tristenpayne2020-web/Grille-talk-keychains/kc/cars/amg_gt63_4door/ref/front.jpg

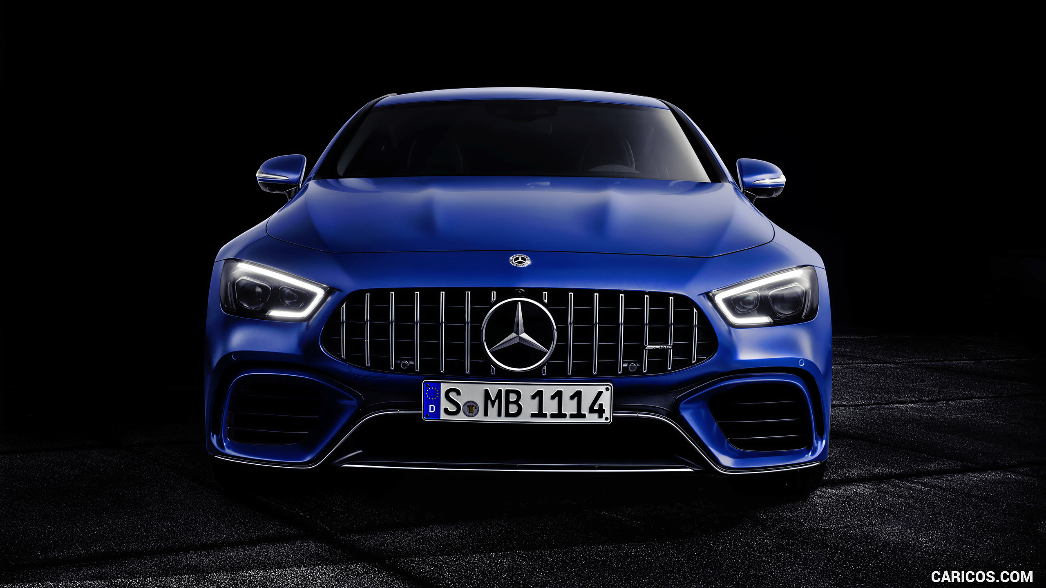
kc/cars/amg_gt63_4door/ref/front.jpg
