tristenpayne2020-web/Grille-talk-keychains/kc/cars/bugatti_chiron/ref/front.jpg

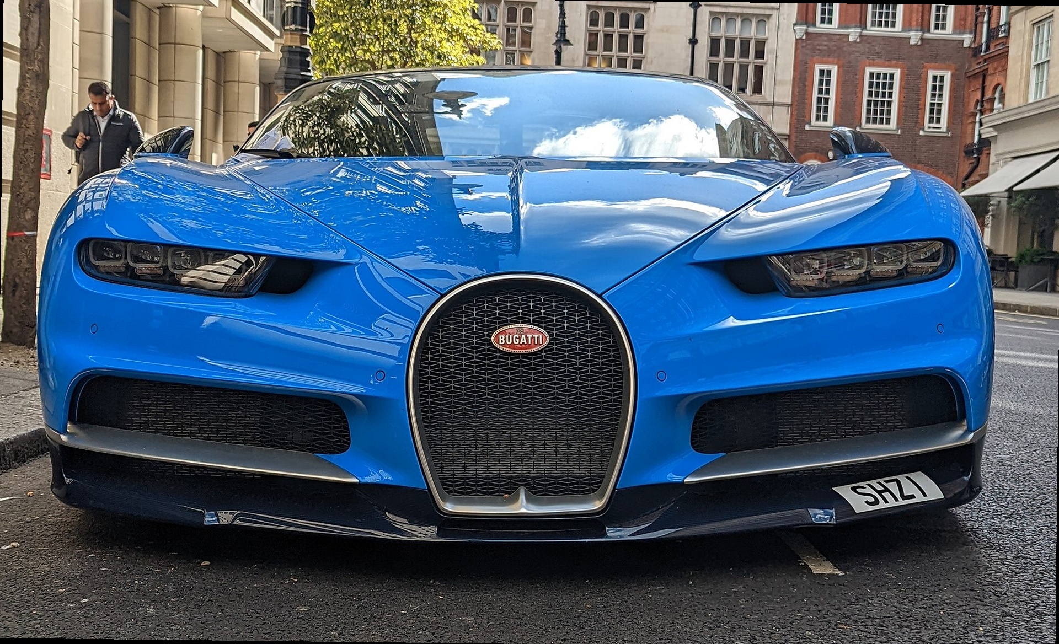
kc/cars/bugatti_chiron/ref/front.jpg
