tristenpayne2020-web/Grille-talk-keychains/kc/cars/c7_z06/ref/cand_blue_show.jpg

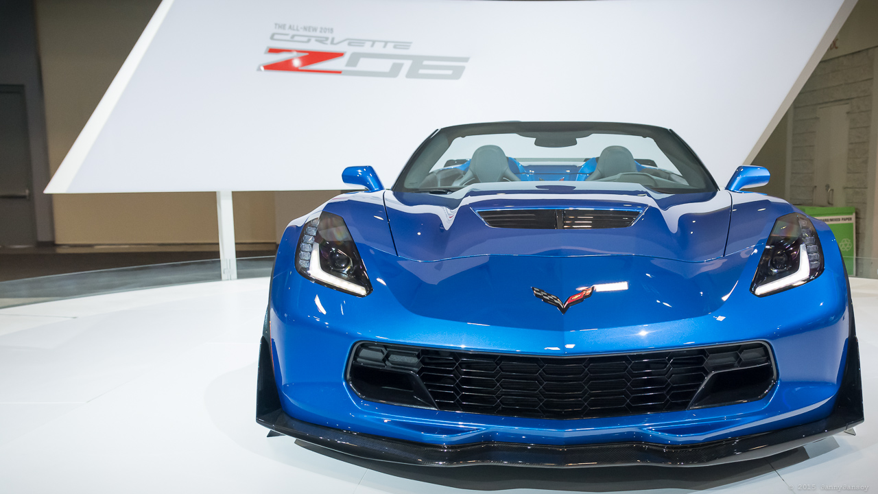
kc/cars/c7_z06/ref/cand_blue_show.jpg
