tristenpayne2020-web/Grille-talk-keychains/kc/cars/c7_z06/ref/front_raw.jpg

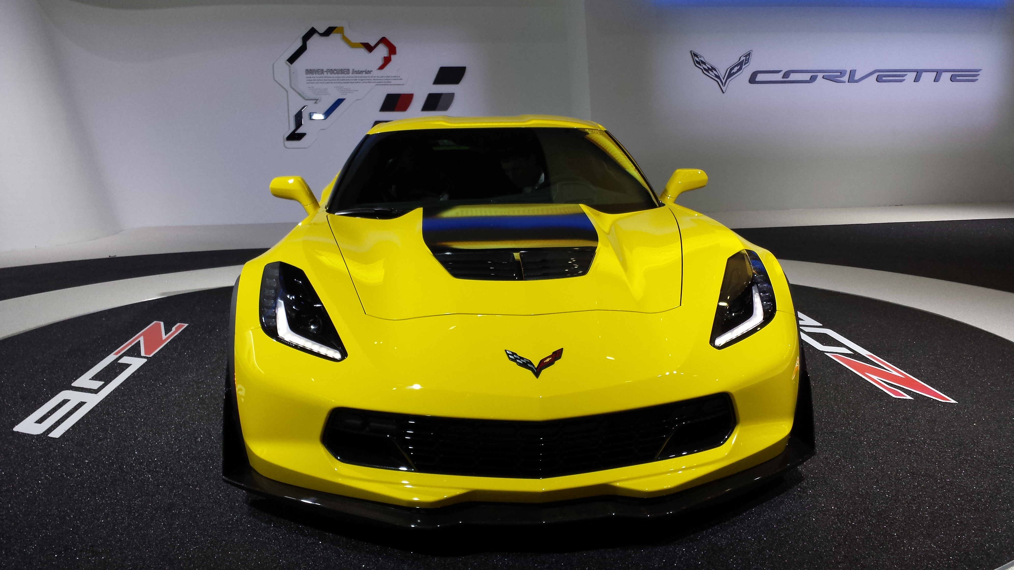
kc/cars/c7_z06/ref/front_raw.jpg
