tristenpayne2020-web/Grille-talk-keychains/kc/cars/c8_corvette/ref/front.jpg

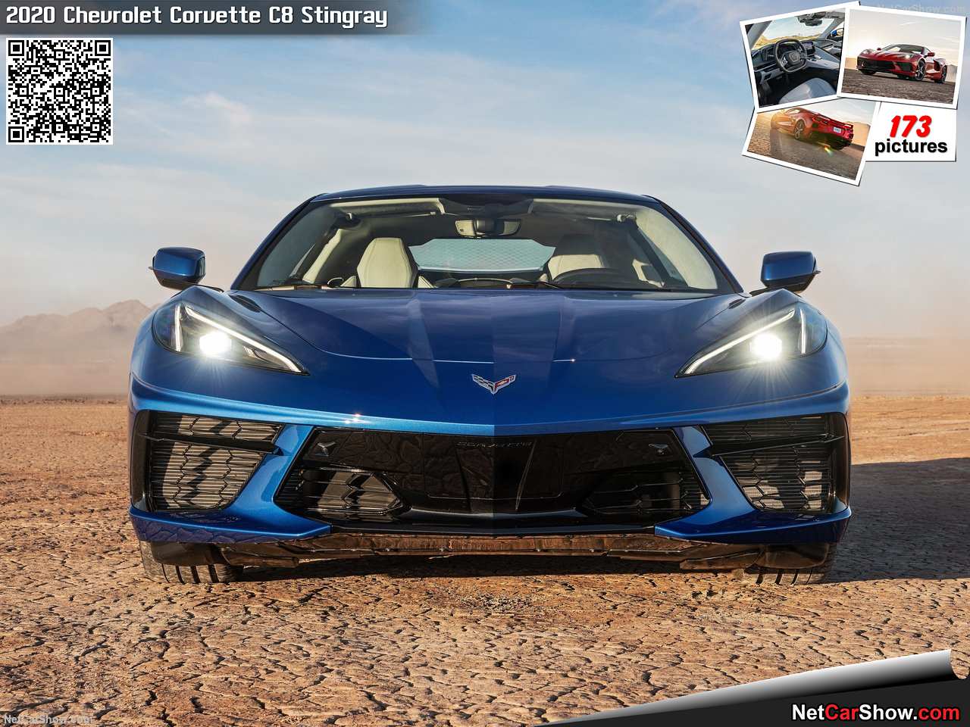
kc/cars/c8_corvette/ref/front.jpg
