tristenpayne2020-web/Grille-talk-keychains/kc/cars/camaro_zl1/ref/front.jpg

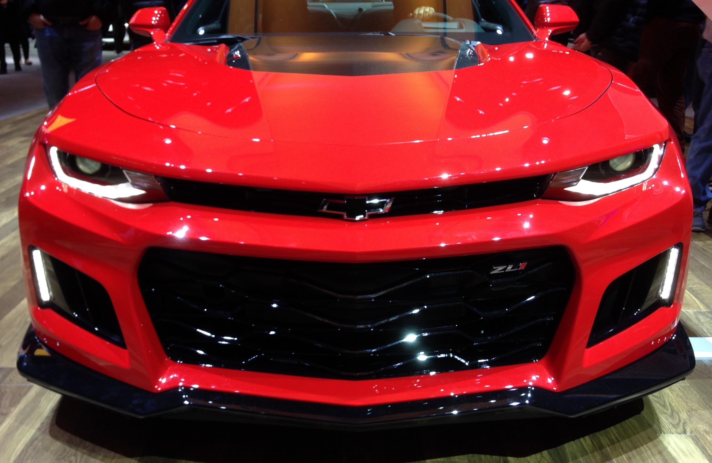
kc/cars/camaro_zl1/ref/front.jpg
