tristenpayne2020-web/Grille-talk-keychains/kc/cars/challenger_hellcat/ref/front.jpg

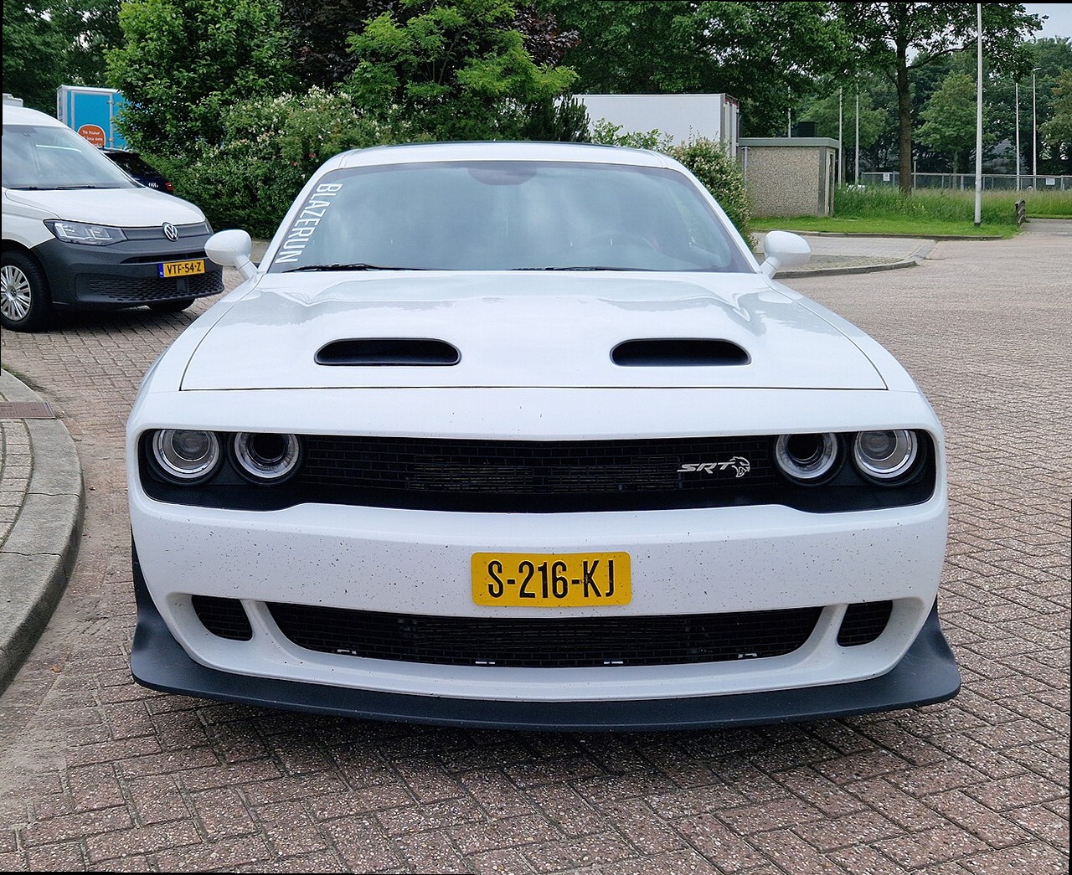
kc/cars/challenger_hellcat/ref/front.jpg
