tristenpayne2020-web/Grille-talk-keychains/kc/cars/charger_srt/ref/front.jpg

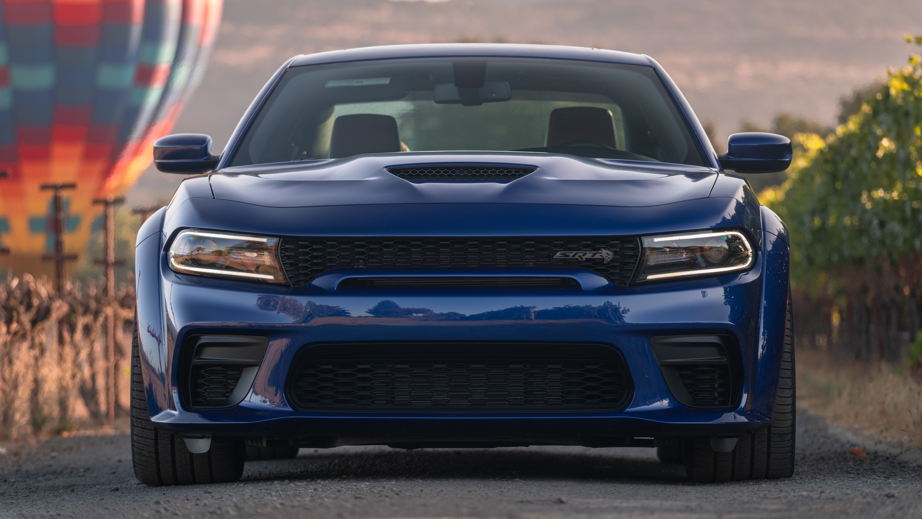
kc/cars/charger_srt/ref/front.jpg
