tristenpayne2020-web/Grille-talk-keychains/kc/cars/civic_11th/ref/front.jpg

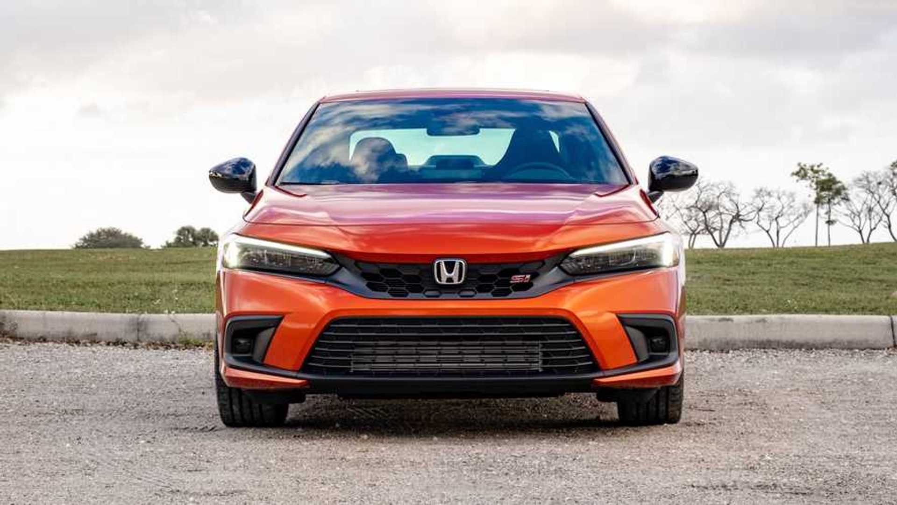
kc/cars/civic_11th/ref/front.jpg
