tristenpayne2020-web/Grille-talk-keychains/kc/cars/ct5v_blackwing/ref/front.jpg

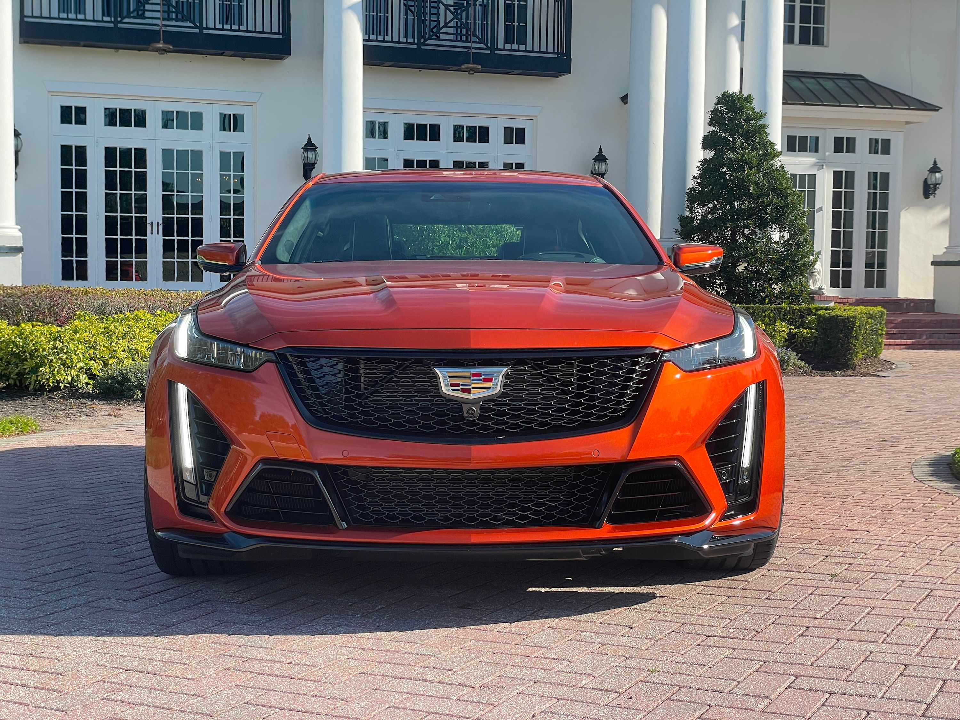
kc/cars/ct5v_blackwing/ref/front.jpg
