tristenpayne2020-web/Grille-talk-keychains/kc/cars/e30_m3/ref/front.jpg

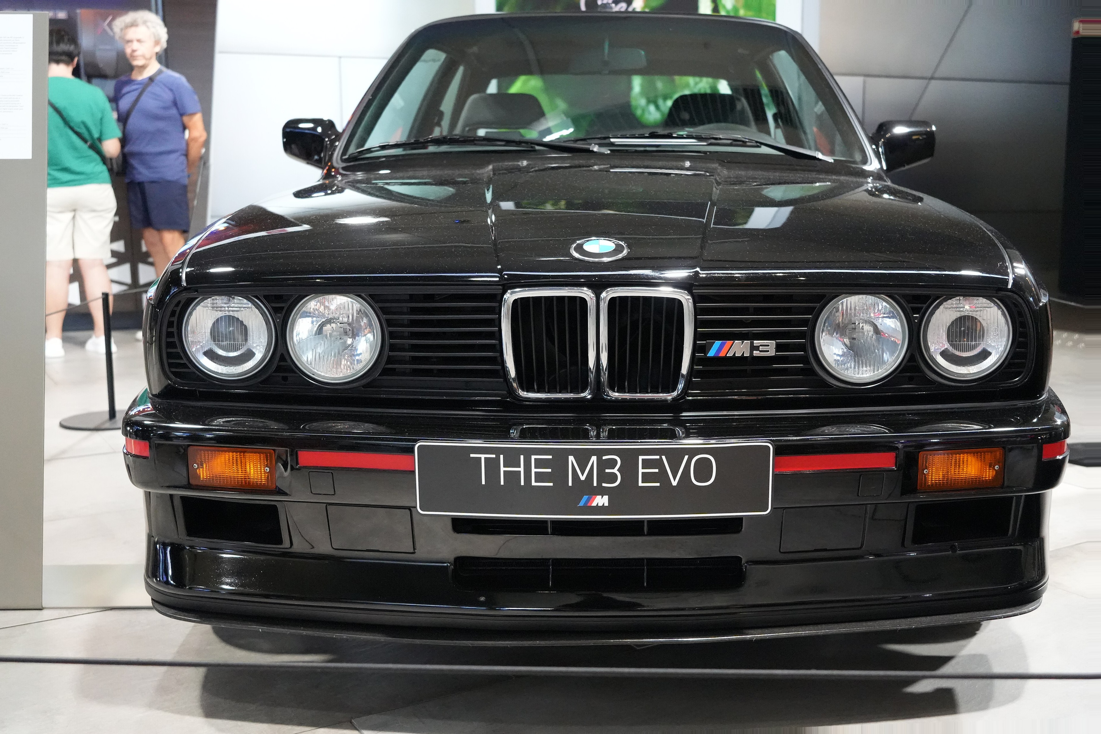
kc/cars/e30_m3/ref/front.jpg
