tristenpayne2020-web/Grille-talk-keychains/kc/cars/f82_m4/ref/front.jpg

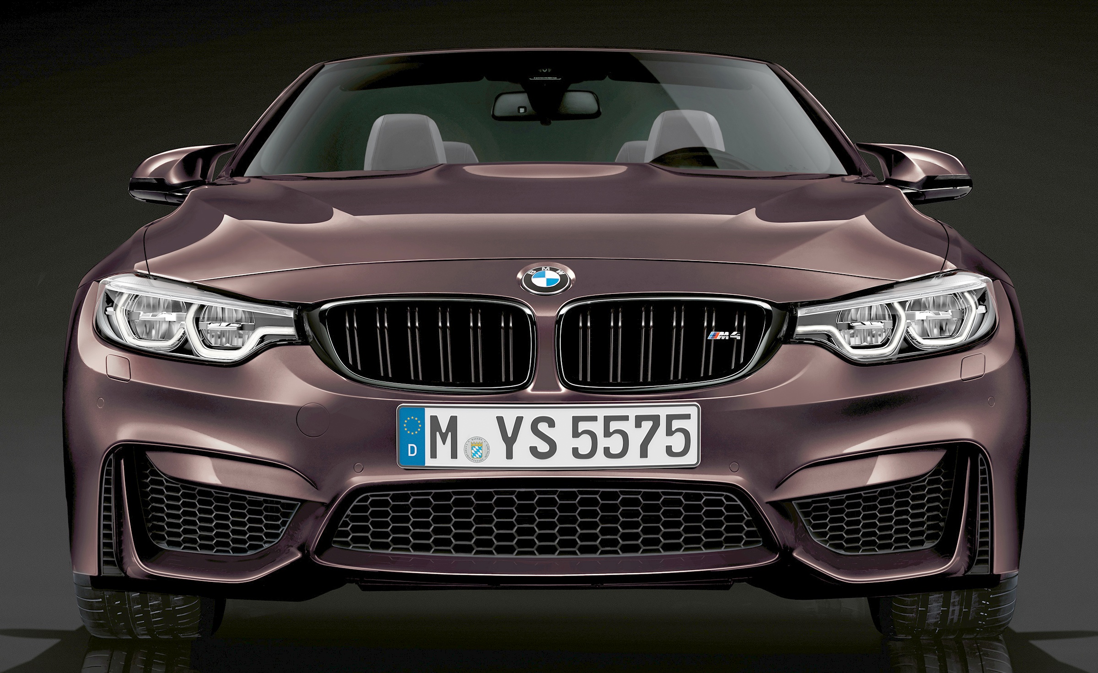
kc/cars/f82_m4/ref/front.jpg
