tristenpayne2020-web/Grille-talk-keychains/kc/cars/f87_m2/ref/front.jpg

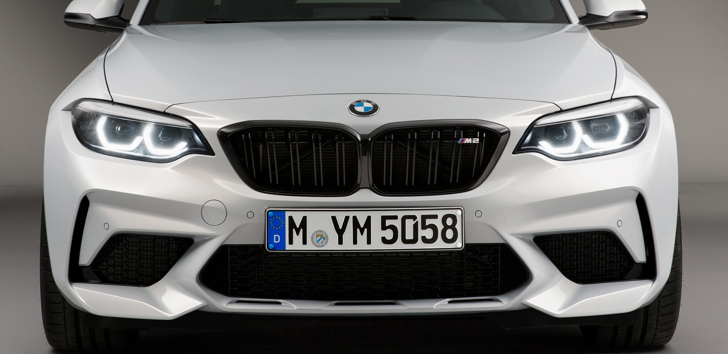
kc/cars/f87_m2/ref/front.jpg
