tristenpayne2020-web/Grille-talk-keychains/kc/cars/f92_m8/ref/front_level.jpg

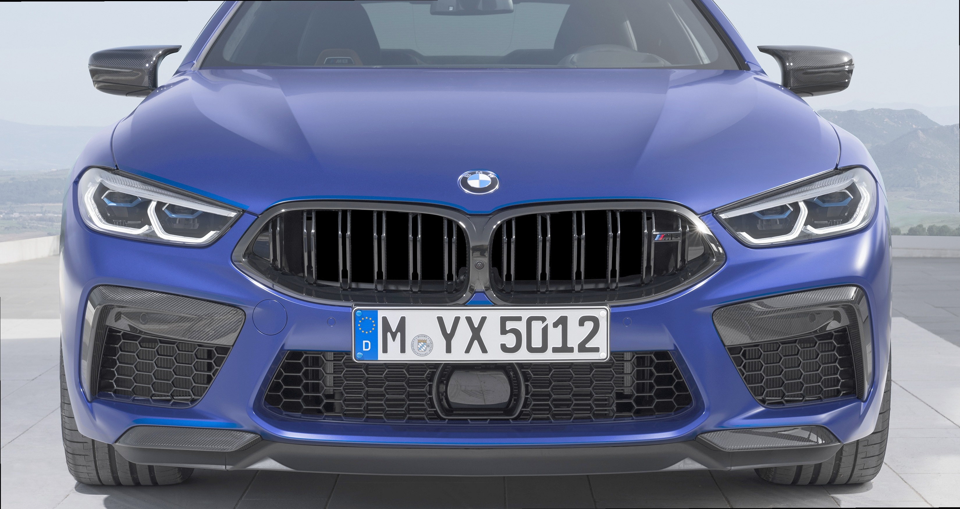
kc/cars/f92_m8/ref/front_level.jpg
