tristenpayne2020-web/Grille-talk-keychains/kc/cars/g20_m340i_lci/ref/front.jpg

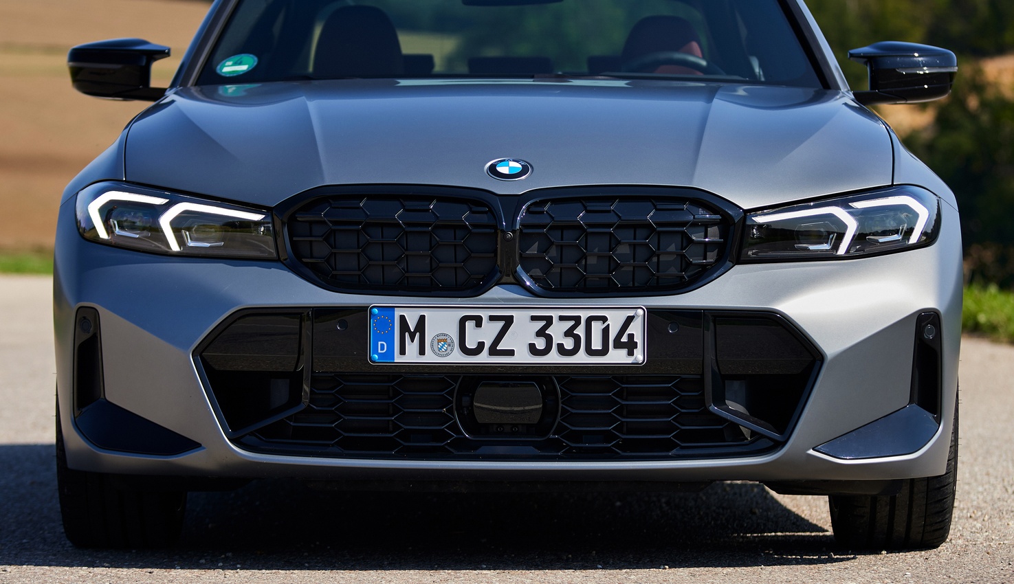
kc/cars/g20_m340i_lci/ref/front.jpg
