tristenpayne2020-web/Grille-talk-keychains/kc/cars/g42_m240i_lci/ref/front.jpg

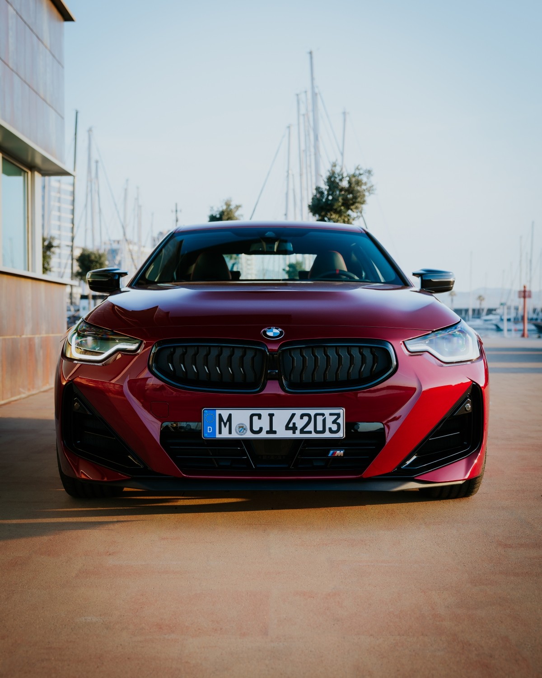
kc/cars/g42_m240i_lci/ref/front.jpg
