tristenpayne2020-web/Grille-talk-keychains/kc/cars/g87_m2/ref/front_warped.png

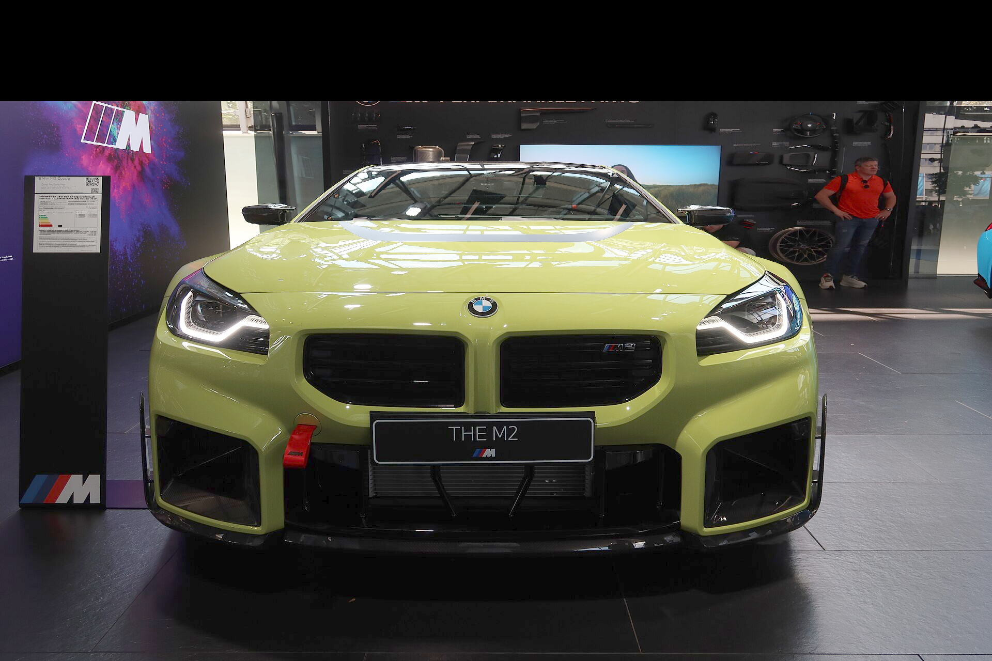
kc/cars/g87_m2/ref/front_warped.png
