tristenpayne2020-web/Grille-talk-keychains/kc/cars/gr86/ref/front.jpg

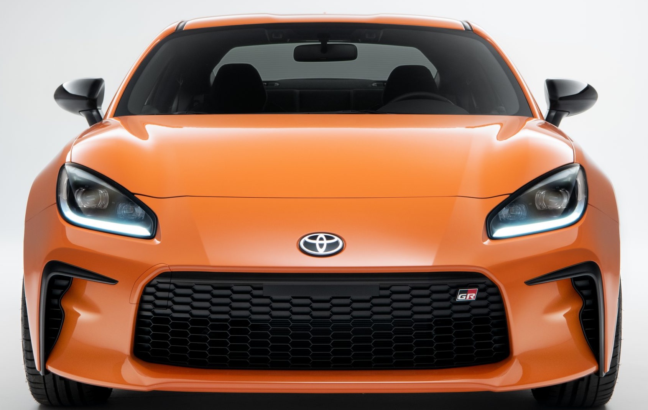
kc/cars/gr86/ref/front.jpg
