tristenpayne2020-web/Grille-talk-keychains/kc/cars/gt3rs_992/ref/front.jpg

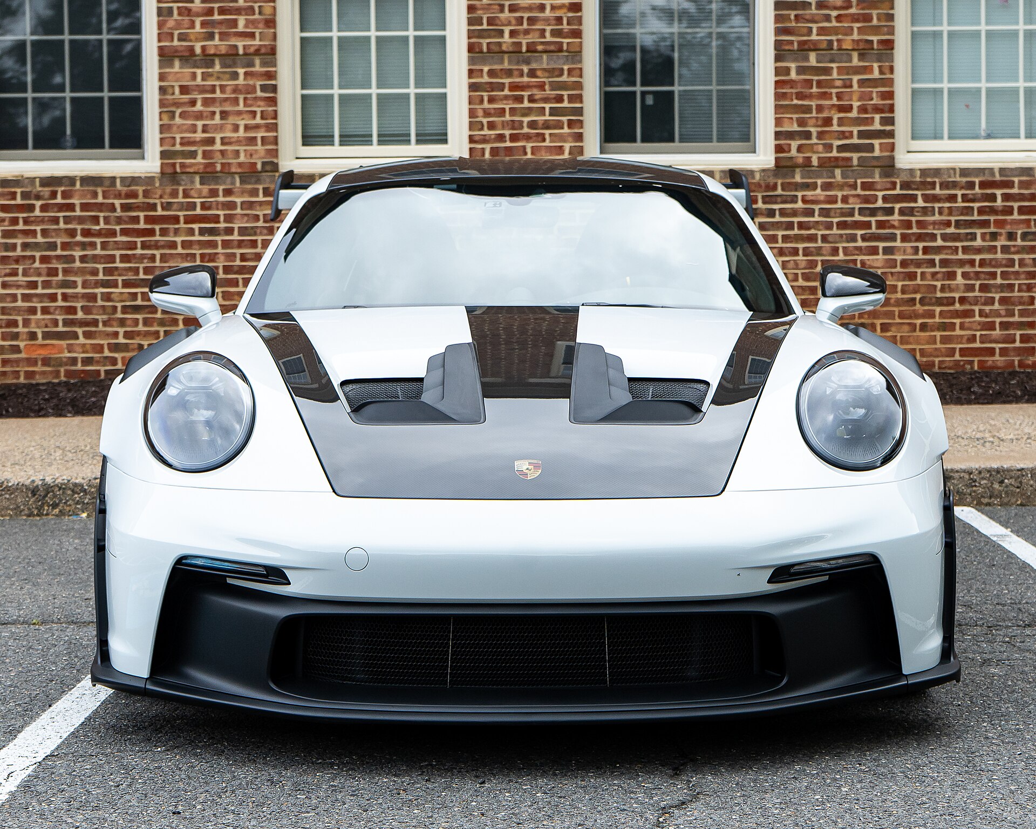
kc/cars/gt3rs_992/ref/front.jpg
