tristenpayne2020-web/Grille-talk-keychains/kc/cars/gt500_mustang/ref/front.jpg

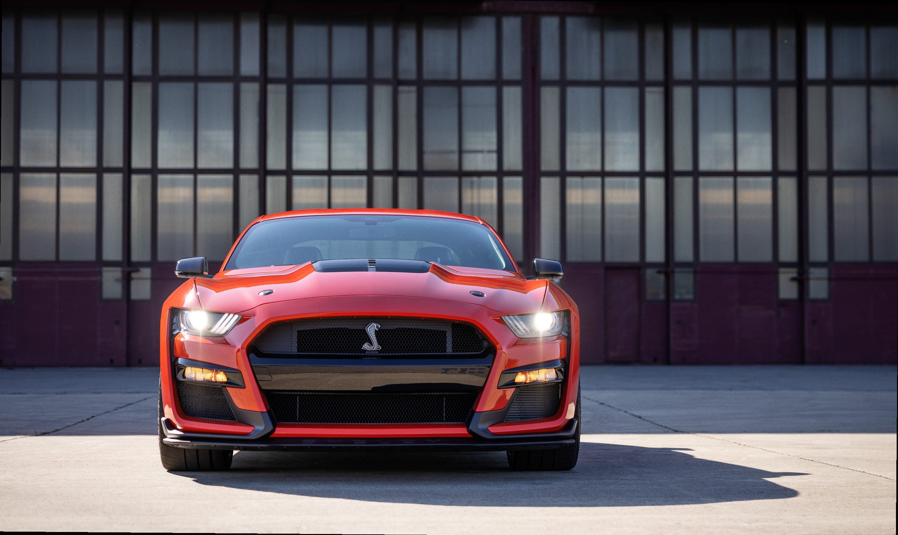
kc/cars/gt500_mustang/ref/front.jpg
