tristenpayne2020-web/Grille-talk-keychains/kc/cars/lambo_urus/ref/front.jpg

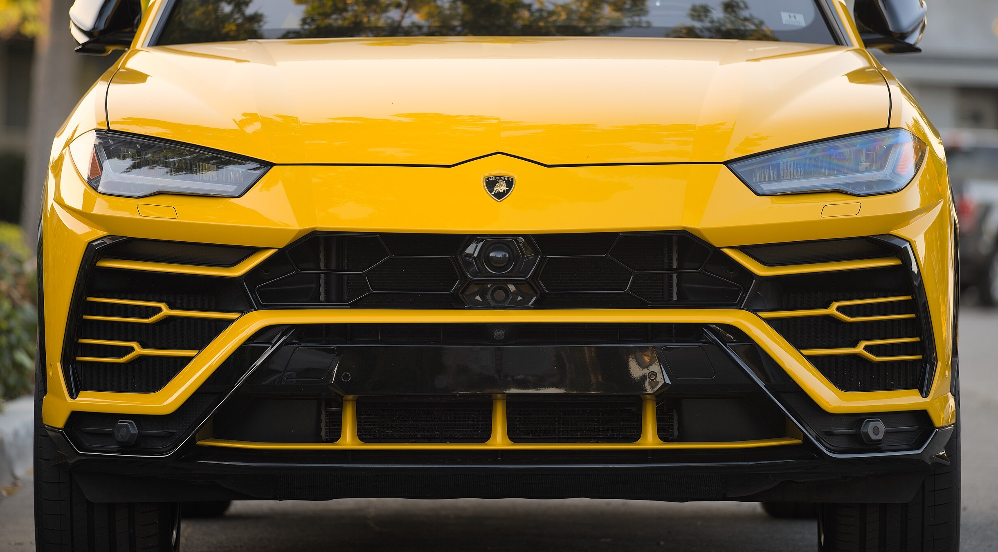
kc/cars/lambo_urus/ref/front.jpg
