tristenpayne2020-web/Grille-talk-keychains/kc/cars/lexus_is350/ref/front.jpg

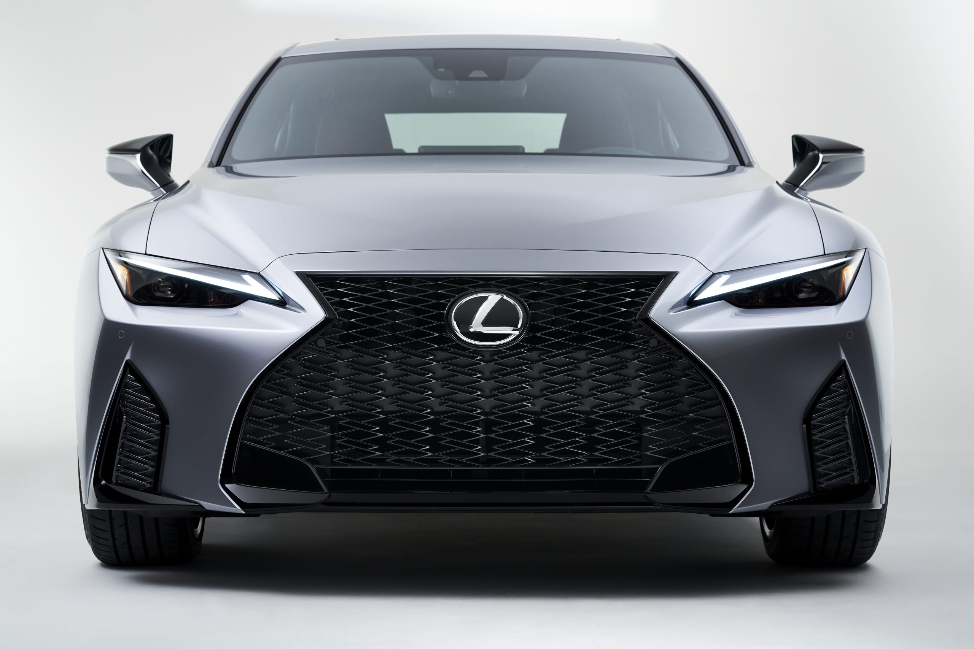
kc/cars/lexus_is350/ref/front.jpg
