tristenpayne2020-web/Grille-talk-keychains/kc/cars/mclaren_720s/ref/front.jpg

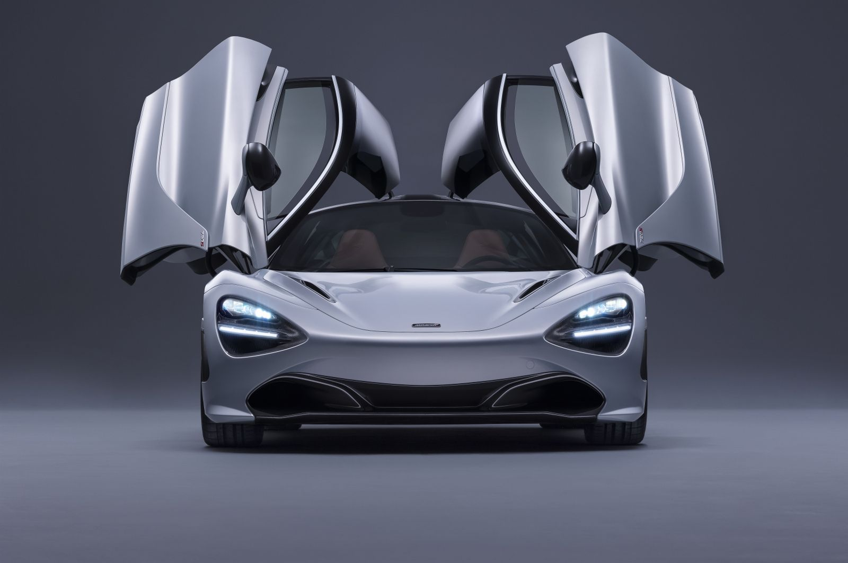
kc/cars/mclaren_720s/ref/front.jpg
