tristenpayne2020-web/Grille-talk-keychains/kc/cars/mk5_supra/ref/front.jpg

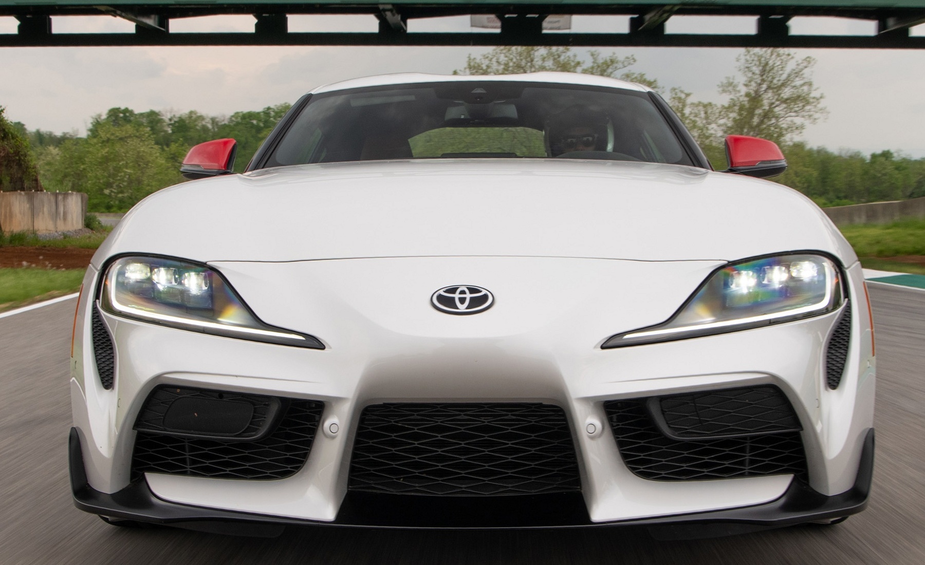
kc/cars/mk5_supra/ref/front.jpg
