tristenpayne2020-web/Grille-talk-keychains/kc/cars/r8_audi/ref/front.jpg

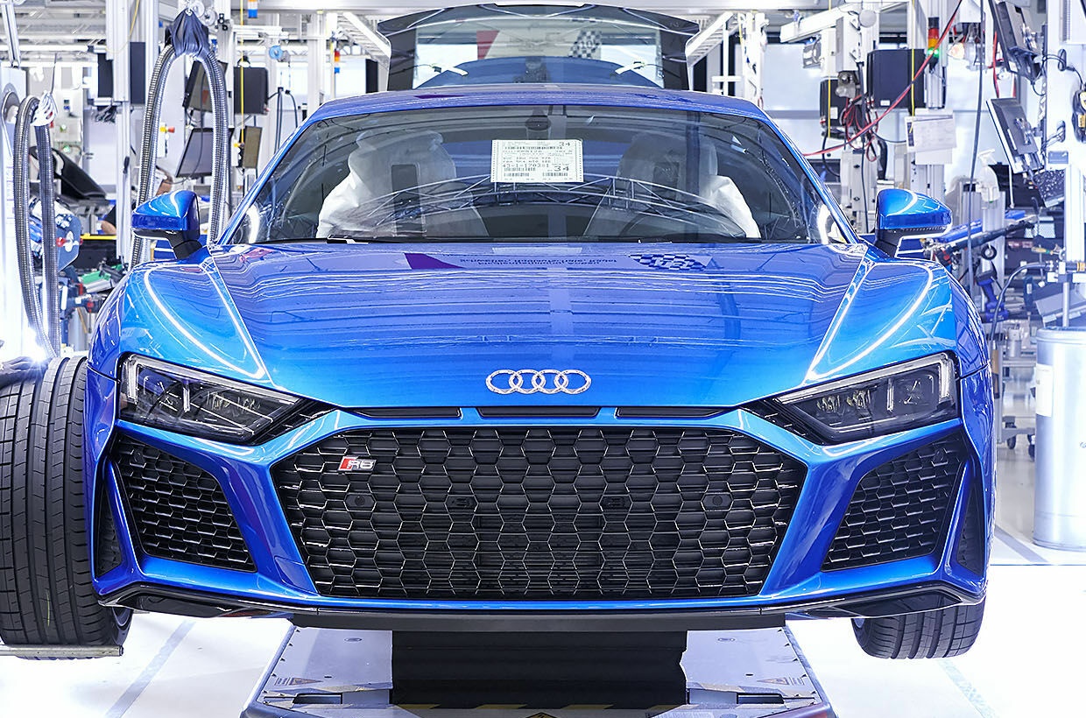
kc/cars/r8_audi/ref/front.jpg
