tristenpayne2020-web/Grille-talk-keychains/kc/cars/r35_gtr/ref/front.jpg

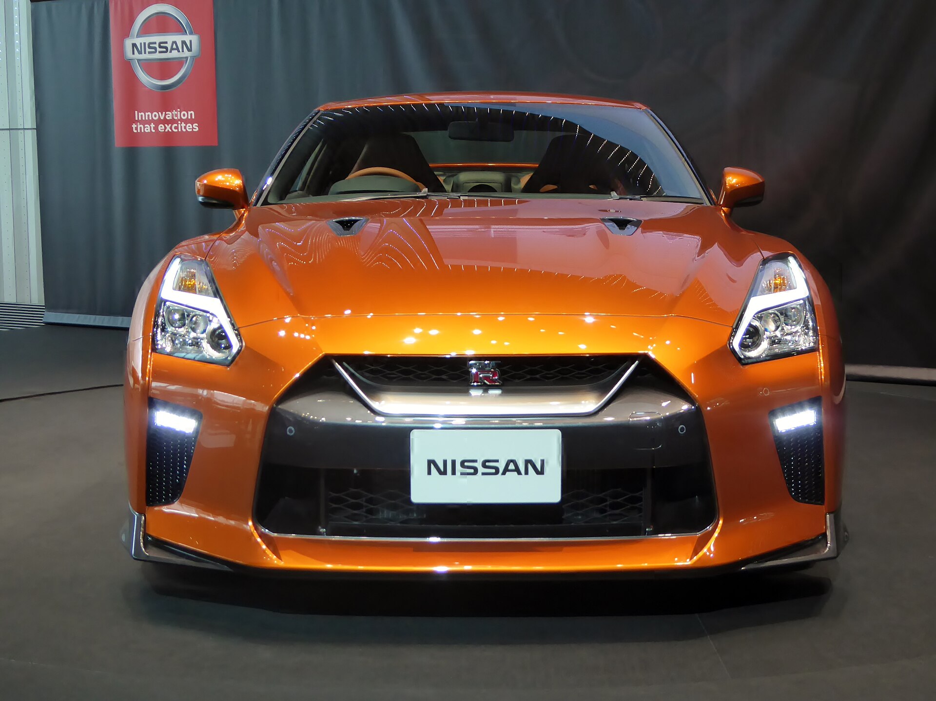
kc/cars/r35_gtr/ref/front.jpg
