tristenpayne2020-web/Grille-talk-keychains/kc/cars/r35_gtr/ref/front_hood085.jpg

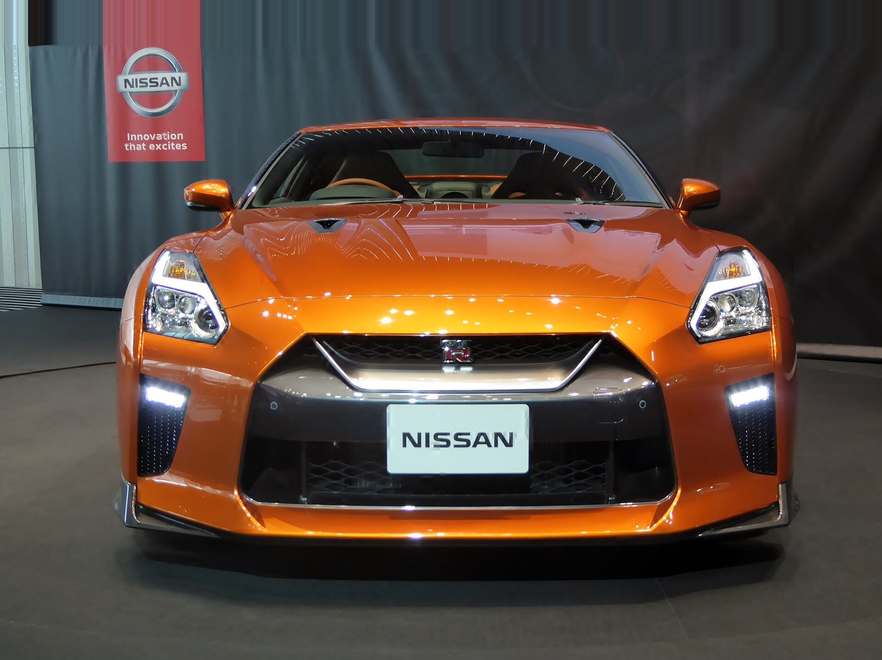
kc/cars/r35_gtr/ref/front_hood085.jpg
