tristenpayne2020-web/Grille-talk-keychains/kc/cars/s650_mustang/ref/front.jpg

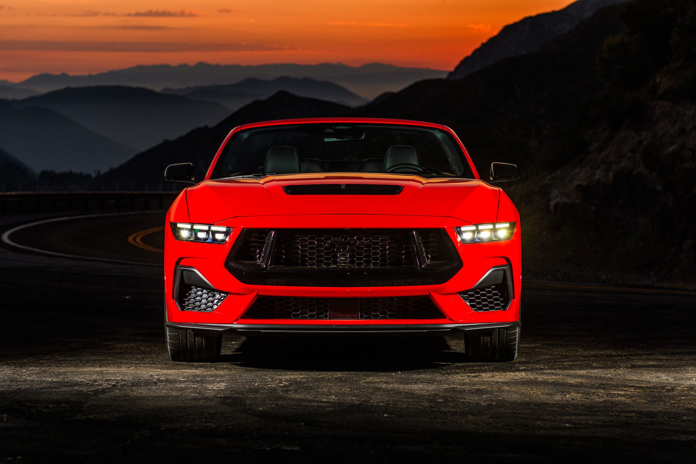
kc/cars/s650_mustang/ref/front.jpg
