tristenpayne2020-web/Grille-talk-keychains/kc/cars/svj_aventador/ref/alt_red_monaco_1146.jpg

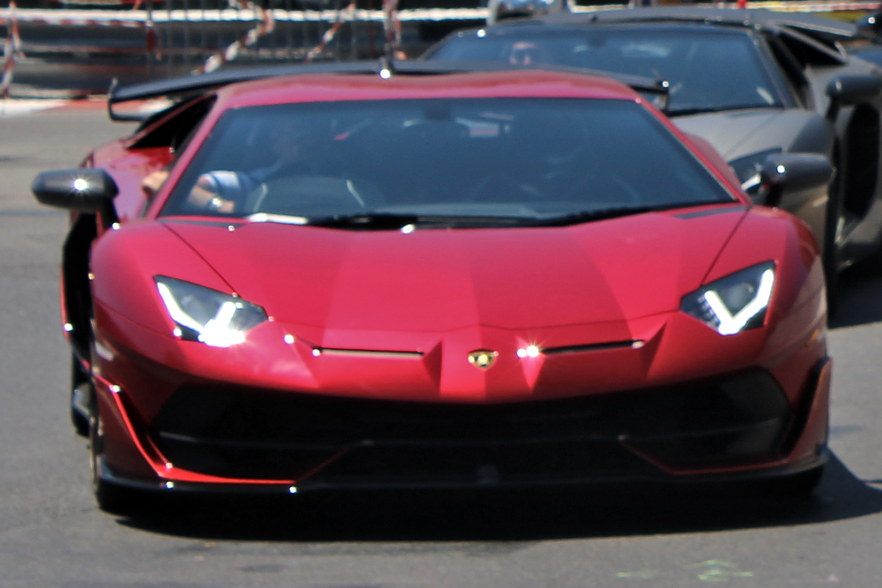
kc/cars/svj_aventador/ref/alt_red_monaco_1146.jpg
