tristenpayne2020-web/Grille-talk-keychains/kc/cars/svj_aventador/ref/front.jpg

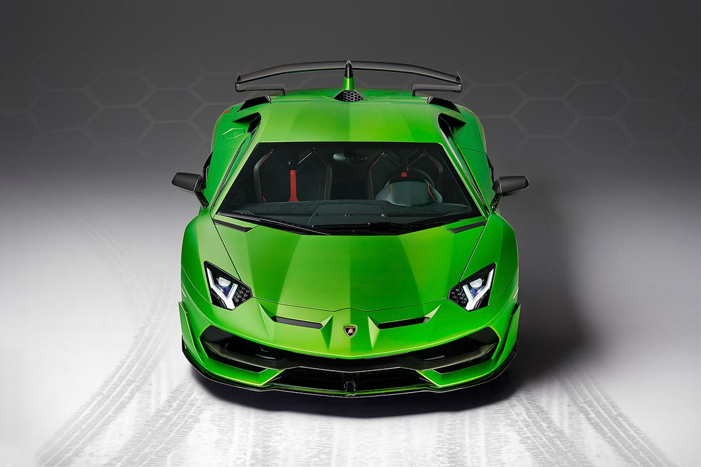
kc/cars/svj_aventador/ref/front.jpg
