tristenpayne2020-web/Grille-talk-keychains/kc/cars/svj_aventador/ref/front_elev.png

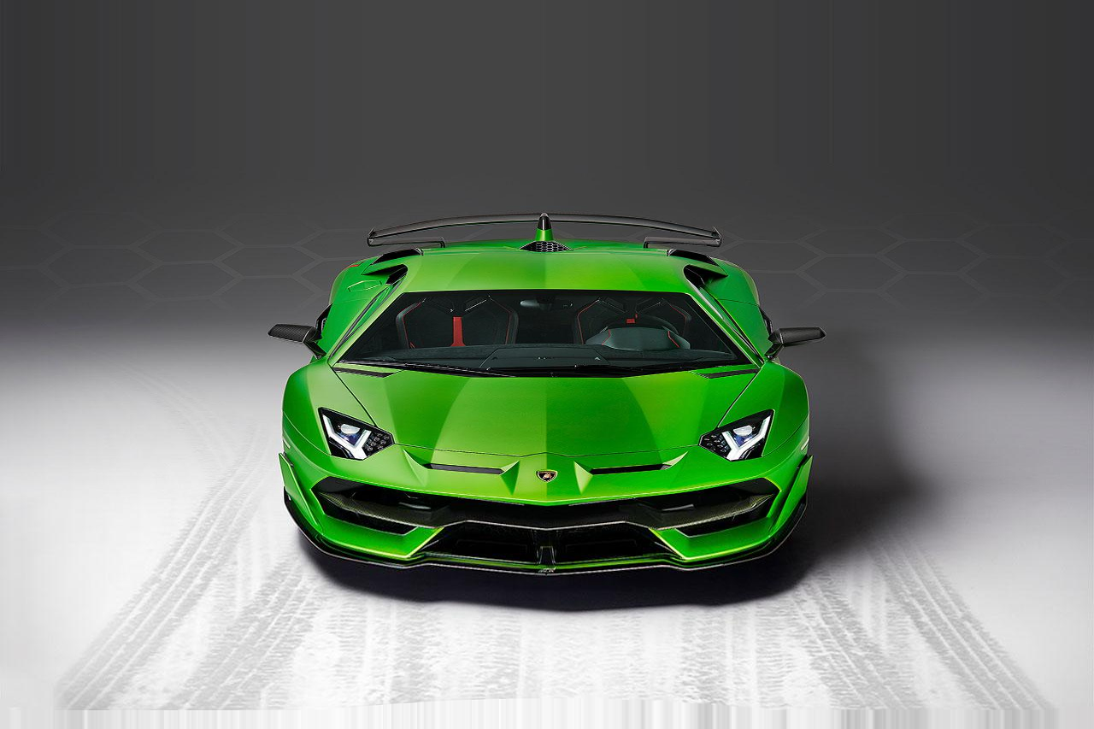
kc/cars/svj_aventador/ref/front_elev.png
