tristenpayne2020-web/Grille-talk-keychains/kc/cars/zonda_cinque/ref/front_press.jpg

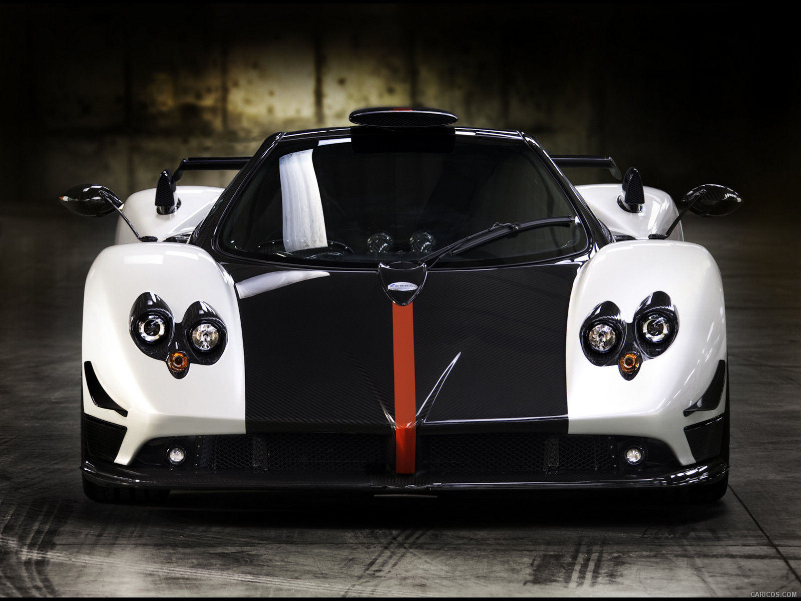
kc/cars/zonda_cinque/ref/front_press.jpg
