tristenpayne2020-web/Grille-talk-keychains/kc/style/g80_face_flat.png

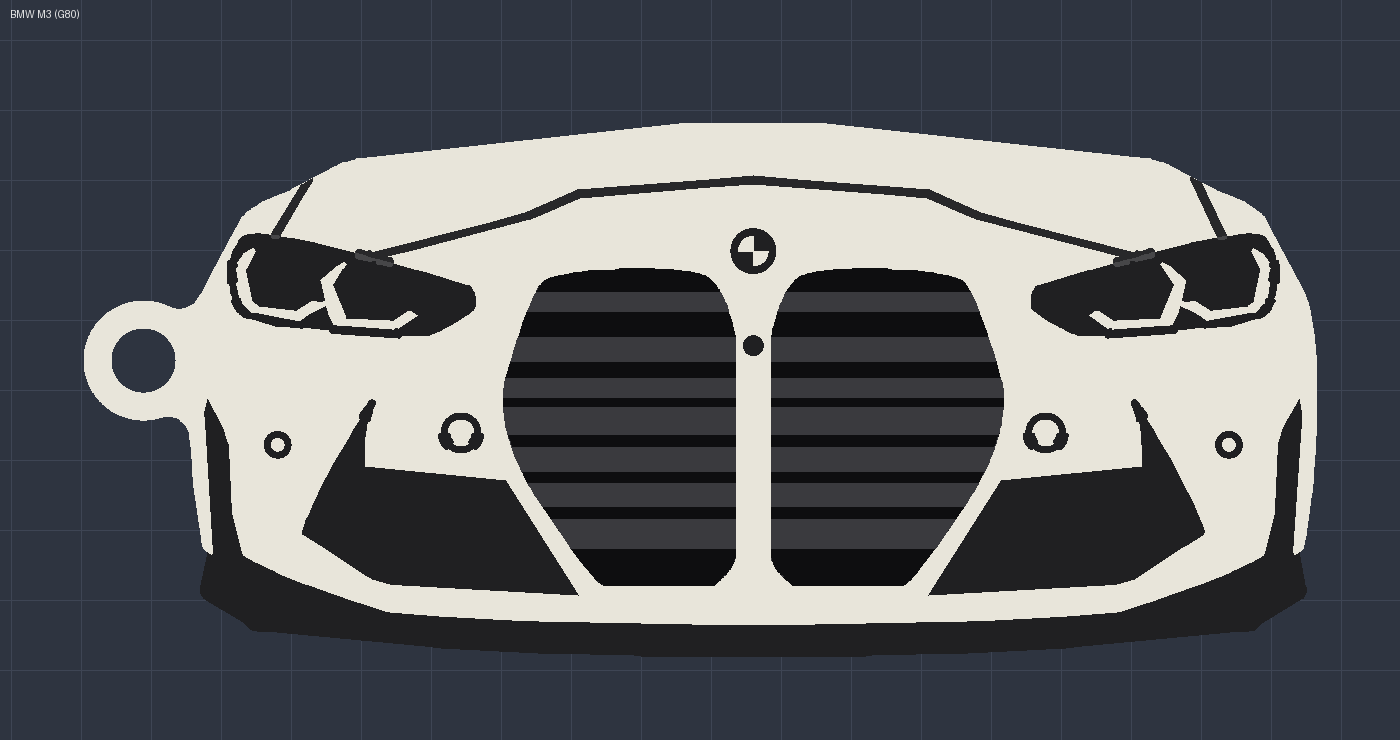
kc/style/g80_face_flat.png
