tristenpayne2020-web/Grille-talk-keychains/kc/style/g80_reference_photo_the_user_traced.png

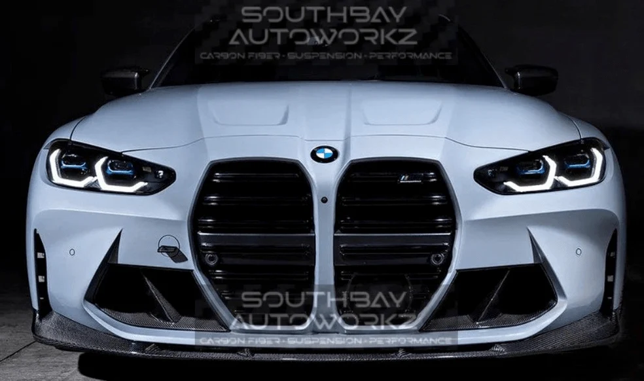
kc/style/g80_reference_photo_the_user_traced.png
