tristenpayne2020-web/Grille-talk-keychains/kc/style/g80_user_keychain_fusion_screenshot.png

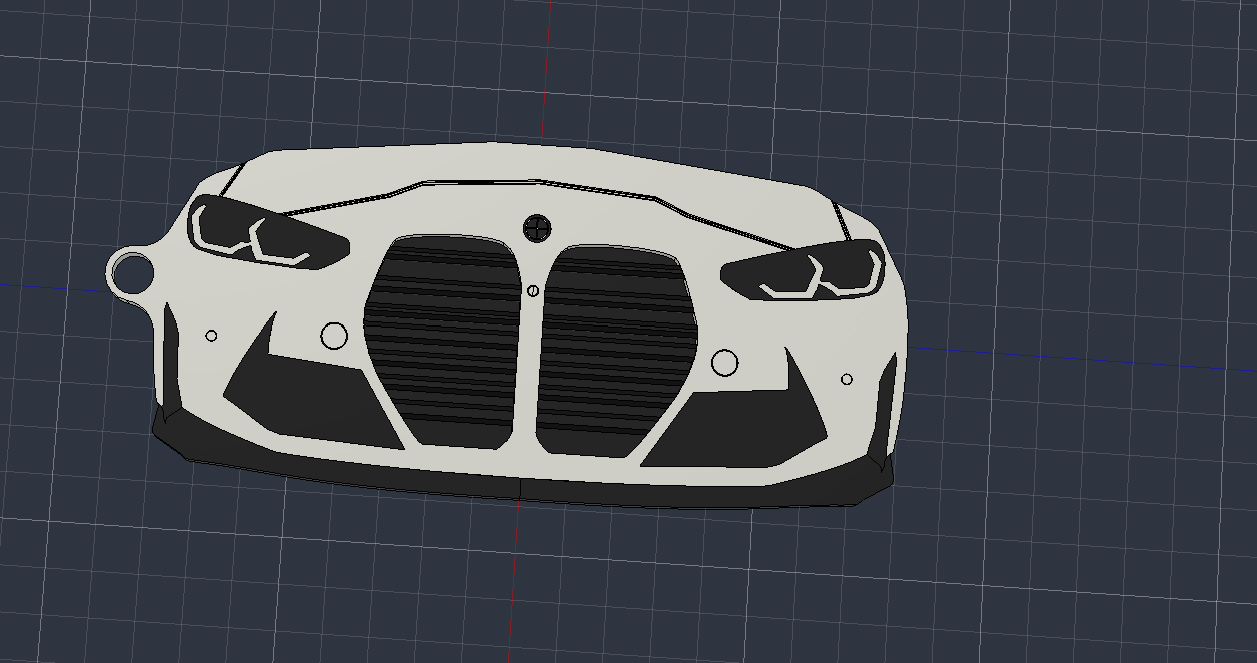
kc/style/g80_user_keychain_fusion_screenshot.png
